fr-kase/wled-cyberppunkclock/SD/background-00.jpg

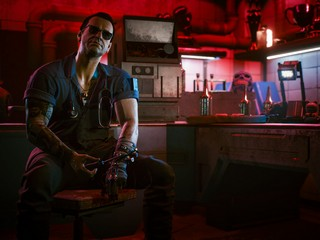
SD/background-00.jpg
