fr-kase/wled-cyberppunkclock/SD/background-01.jpg

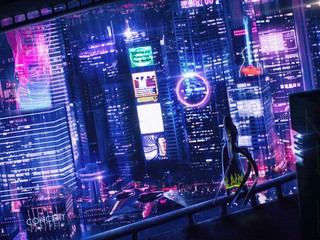
SD/background-01.jpg
