fr-kase/wled-cyberppunkclock/SD/background-02.jpg

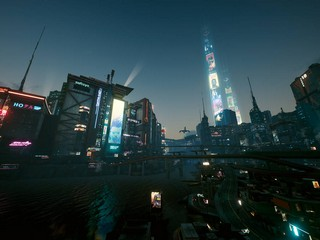
SD/background-02.jpg
