fr-kase/wled-cyberppunkclock/SD/background-03.jpg

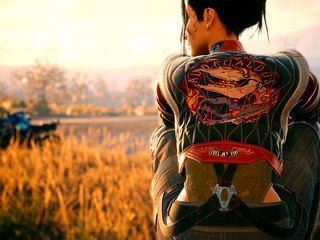
SD/background-03.jpg
