fr-kase/wled-cyberppunkclock/SD/background-04.jpg

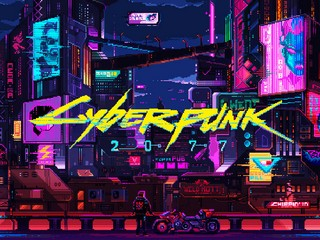
SD/background-04.jpg
