fr-kase/wled-cyberppunkclock/SD/background-05.jpg

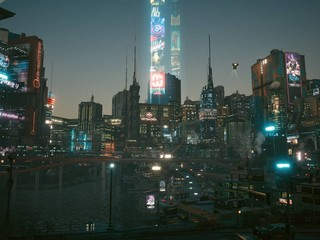
SD/background-05.jpg
