fr-kase/wled-cyberppunkclock/SD/background-06.jpg

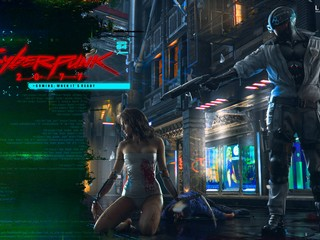
SD/background-06.jpg
