fr-kase/wled-cyberppunkclock/SD/background-07.jpg

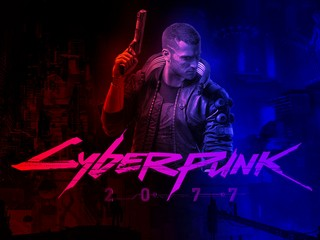
SD/background-07.jpg
