fr-kase/wled-cyberppunkclock/SD/background-08.jpg

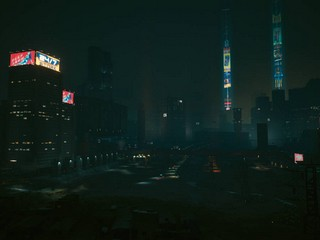
SD/background-08.jpg
