fr-kase/wled-cyberppunkclock/SD/background-09.jpg

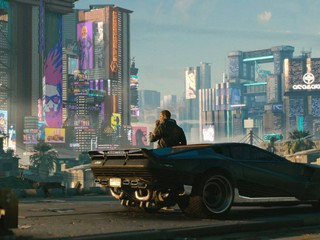
SD/background-09.jpg
