fr-kase/wled-cyberppunkclock/SD/background-10.jpg

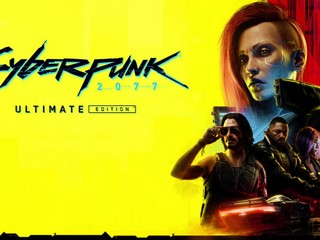
SD/background-10.jpg
