fr-kase/wled-cyberppunkclock/SD/background-11.jpg

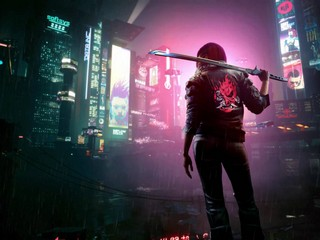
SD/background-11.jpg
