fr-kase/wled-cyberppunkclock/SD/background-12.jpg

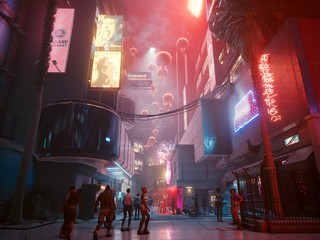
SD/background-12.jpg
