fr-kase/wled-cyberppunkclock/SD/background-13.jpg

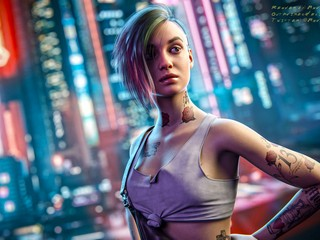
SD/background-13.jpg
