fr-kase/wled-cyberppunkclock/SD/background-14.jpg

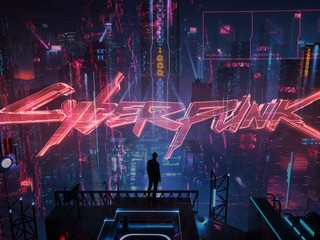
SD/background-14.jpg
