fr-kase/wled-cyberppunkclock/SD/background-15.jpg

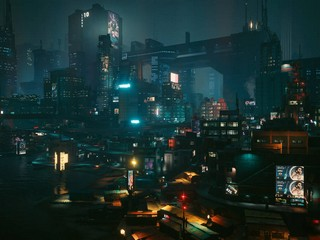
SD/background-15.jpg
