fr-kase/wled-cyberppunkclock/SD/background-16.jpg

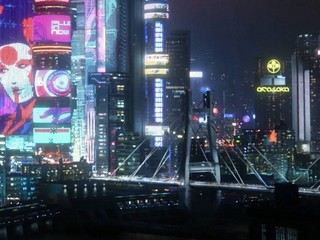
SD/background-16.jpg
