fr-kase/wled-cyberppunkclock/SD/background-17.jpg

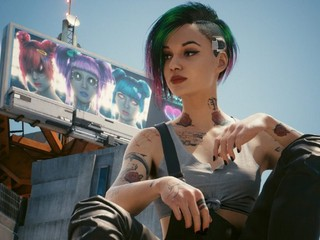
SD/background-17.jpg
