fr-kase/wled-cyberppunkclock/SD/background-18.jpg

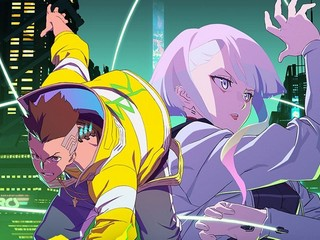
SD/background-18.jpg
