fr-kase/wled-cyberppunkclock/SD/background-19.jpg

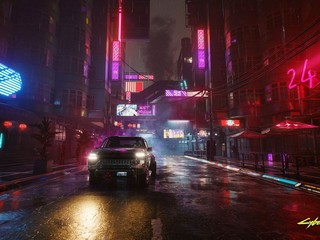
SD/background-19.jpg
