fr-kase/wled-cyberppunkclock/SD/background-20.jpg

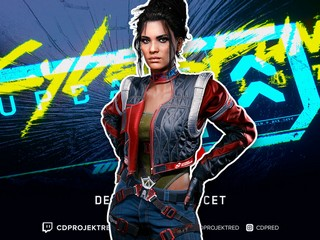
SD/background-20.jpg
