fr-kase/wled-cyberppunkclock/SD/background-23.jpg

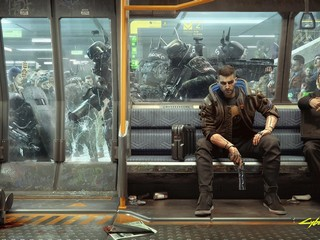
SD/background-23.jpg
